Nikhil-Krishnamurthy/OVERBoard/Code - Custom C++/lvgl-master/tests/ref_imgs/draw/render/al88/demo_render_image_normal_1_opa_255.png

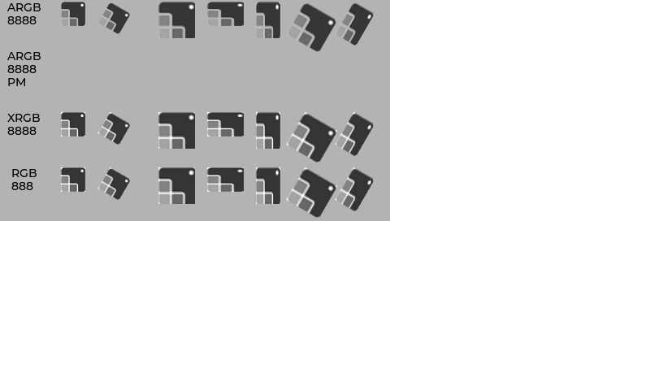
Code - Custom C++/lvgl-master/tests/ref_imgs/draw/render/al88/demo_render_image_normal_1_opa_255.png
