Nikhil-Krishnamurthy/OVERBoard/Code - Custom C++/lvgl-master/tests/ref_imgs/draw/render/al88/demo_render_image_recolor_1_opa_128.png

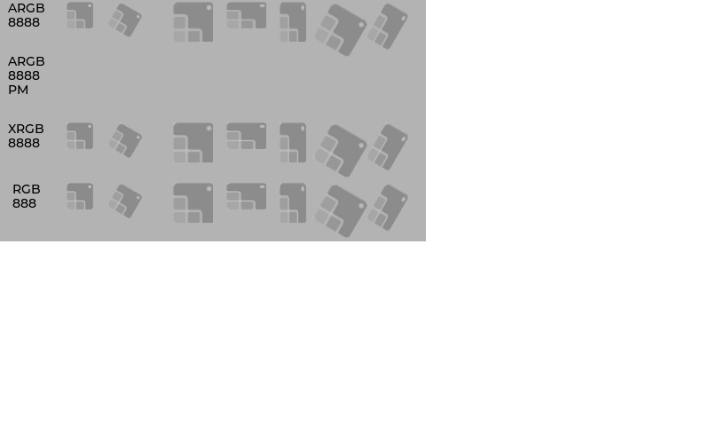
Code - Custom C++/lvgl-master/tests/ref_imgs/draw/render/al88/demo_render_image_recolor_1_opa_128.png
