Nikhil-Krishnamurthy/OVERBoard/Code - Custom C++/lvgl-master/tests/ref_imgs/draw/render/al88/demo_render_line_opa_128.png

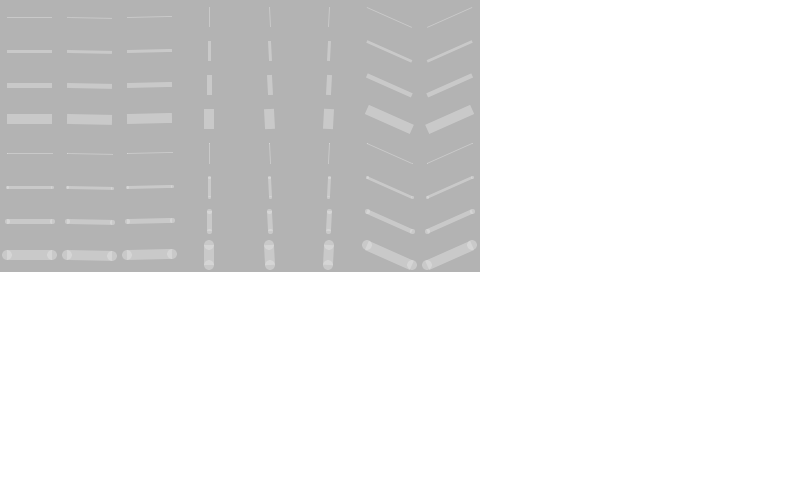
Code - Custom C++/lvgl-master/tests/ref_imgs/draw/render/al88/demo_render_line_opa_128.png
