Nikhil-Krishnamurthy/OVERBoard/Code - Custom C++/lvgl-master/tests/ref_imgs/draw/render/argb8888/demo_render_blend_mode_opa_128.png

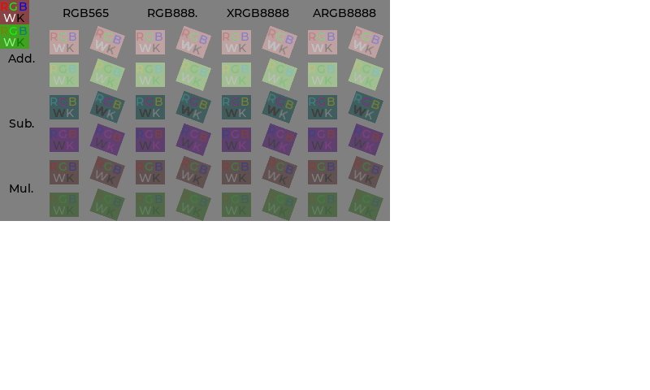
Code - Custom C++/lvgl-master/tests/ref_imgs/draw/render/argb8888/demo_render_blend_mode_opa_128.png
