Nikhil-Krishnamurthy/OVERBoard/Code - Custom C++/lvgl-master/tests/ref_imgs/draw/render/argb8888/demo_render_layer_normal_opa_255.png

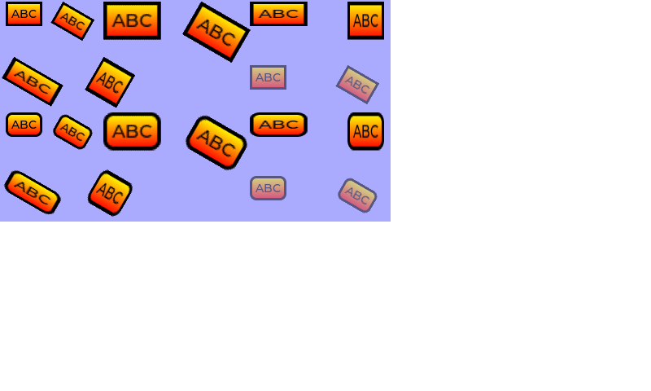
Code - Custom C++/lvgl-master/tests/ref_imgs/draw/render/argb8888/demo_render_layer_normal_opa_255.png
