Nikhil-Krishnamurthy/OVERBoard/Code - Custom C++/lvgl-master/tests/ref_imgs/draw/render/argb8888/demo_render_linear_gradient_opa_128.png

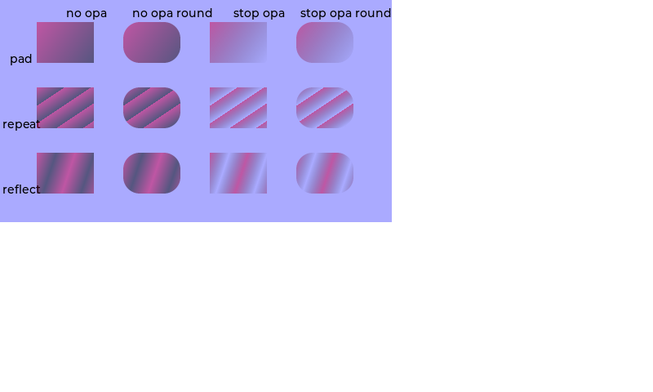
Code - Custom C++/lvgl-master/tests/ref_imgs/draw/render/argb8888/demo_render_linear_gradient_opa_128.png
