Nikhil-Krishnamurthy/OVERBoard/Code - Custom C++/lvgl-master/tests/ref_imgs/draw/render/argb8888_premultiplied/demo_render_line_opa_255.png

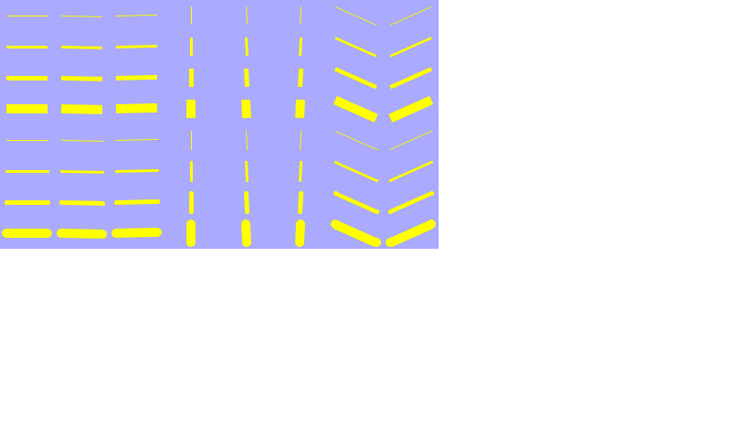
Code - Custom C++/lvgl-master/tests/ref_imgs/draw/render/argb8888_premultiplied/demo_render_line_opa_255.png
