Nikhil-Krishnamurthy/OVERBoard/Code - Custom C++/lvgl-master/tests/ref_imgs/draw/render/i1/demo_render_image_normal_2_opa_255.png

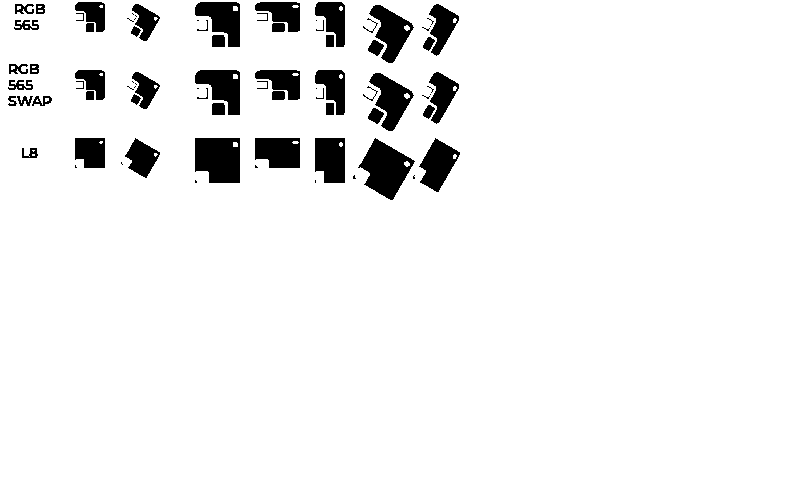
Code - Custom C++/lvgl-master/tests/ref_imgs/draw/render/i1/demo_render_image_normal_2_opa_255.png
