Nikhil-Krishnamurthy/OVERBoard/Code - Custom C++/lvgl-master/tests/ref_imgs/draw/render/i1/demo_render_text_opa_192.png

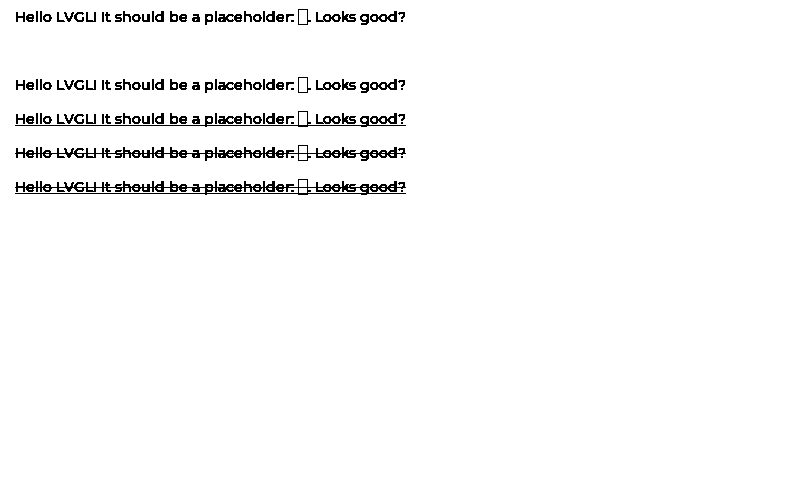
Code - Custom C++/lvgl-master/tests/ref_imgs/draw/render/i1/demo_render_text_opa_192.png
