Nikhil-Krishnamurthy/OVERBoard/Code - Custom C++/lvgl-master/tests/ref_imgs/draw/render/rgb565_swapped/demo_render_arc_image_opa_255.png

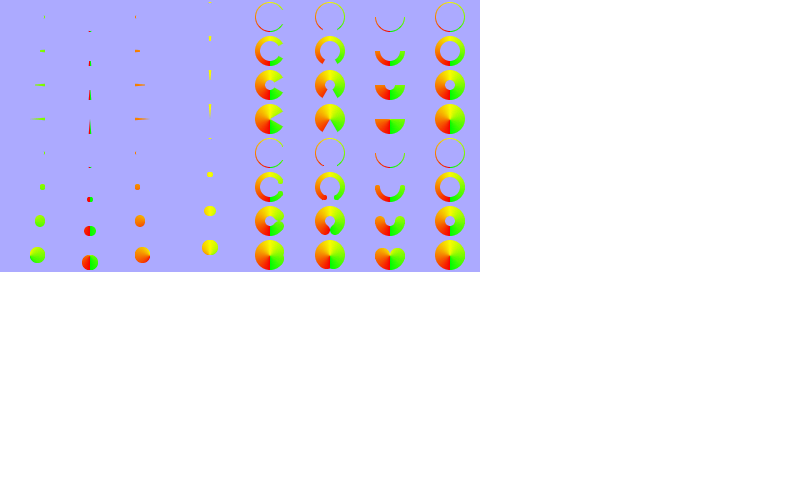
Code - Custom C++/lvgl-master/tests/ref_imgs/draw/render/rgb565_swapped/demo_render_arc_image_opa_255.png
