Nikhil-Krishnamurthy/OVERBoard/Code - Custom C++/lvgl-master/tests/ref_imgs_vg_lite/draw/render/argb1555/demo_render_line_opa_128.png

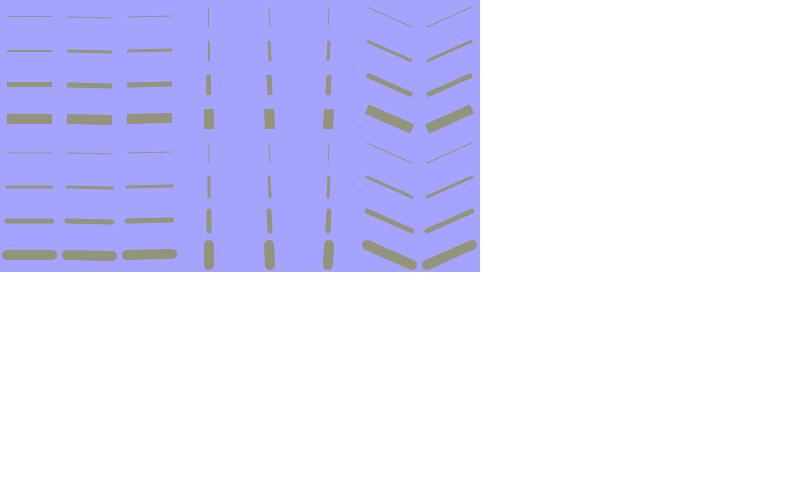
Code - Custom C++/lvgl-master/tests/ref_imgs_vg_lite/draw/render/argb1555/demo_render_line_opa_128.png
