Nikhil-Krishnamurthy/OVERBoard/Code - Custom C++/lvgl-master/tests/ref_imgs_vg_lite/draw/render/argb2222/demo_render_fill_opa_128.png

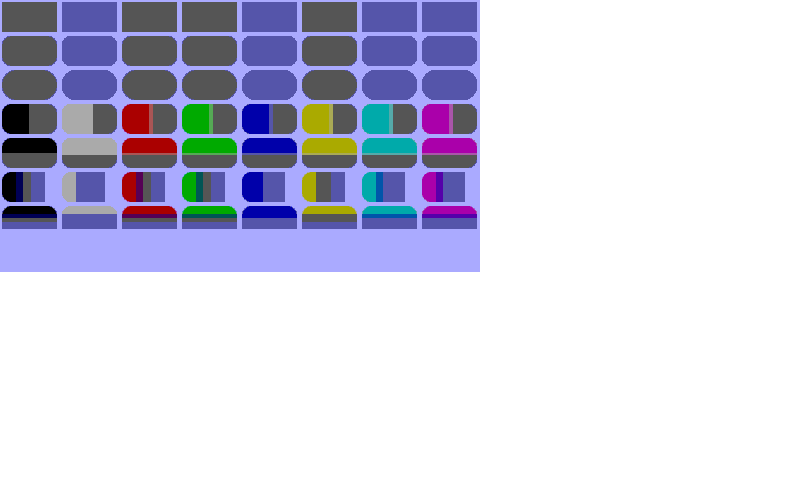
Code - Custom C++/lvgl-master/tests/ref_imgs_vg_lite/draw/render/argb2222/demo_render_fill_opa_128.png
