Nikhil-Krishnamurthy/OVERBoard/Code - Custom C++/lvgl-master/tests/ref_imgs_vg_lite/draw/render/argb8888/demo_render_text_opa_128.png

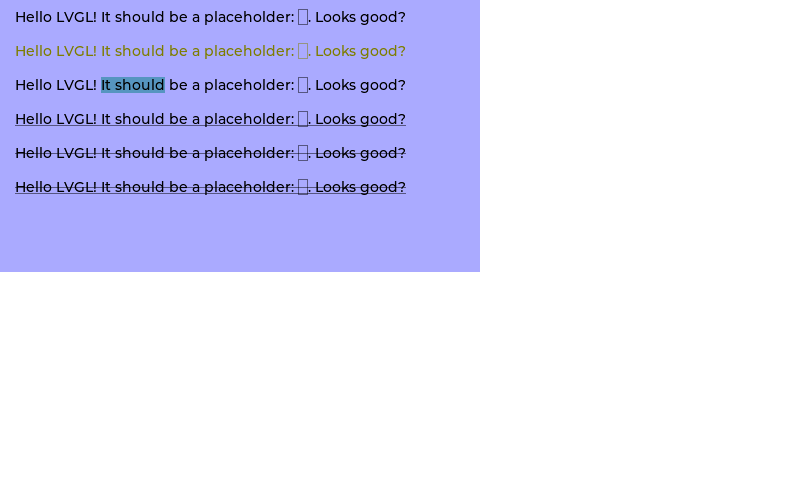
Code - Custom C++/lvgl-master/tests/ref_imgs_vg_lite/draw/render/argb8888/demo_render_text_opa_128.png
