Nikhil-Krishnamurthy/OVERBoard/Code - Custom C++/lvgl-master/docs/src/_static/images/clip_corner_1_problem_being_solved.png

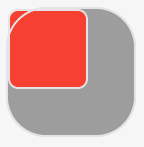
Code - Custom C++/lvgl-master/docs/src/_static/images/clip_corner_1_problem_being_solved.png
