Nikhil-Krishnamurthy/OVERBoard/Code - Custom C++/spi_control.cpp

#include "spi_control.h"
#include <stdio.h>
#include "pico/stdlib.h"
#include "hardware/spi.h"


#define SPI_PORT spi0
#define PIN_MISO 16
#define PIN_CS   17
#define PIN_SCK  18
#define PIN_MOSI 19


spi_control::spi_control()
{

}

spi_control::~spi_control()
{

}

void spi_control::spi_init_custom(){
    spi_init(SPI_PORT, 1000*1000);
    gpio_set_function(PIN_MISO, GPIO_FUNC_SPI);
    gpio_set_function(PIN_CS,   GPIO_FUNC_SIO);
    gpio_set_function(PIN_SCK,  GPIO_FUNC_SPI);
    gpio_set_function(PIN_MOSI, GPIO_FUNC_SPI);
    
    // Chip select is active-low, so we'll initialise it to a driven-high state
    gpio_set_dir(PIN_CS, GPIO_OUT);
    gpio_put(PIN_CS, 1);
}
